LARobotics/LAR-MSL/Code/2023/Images/git_msl_BS.png

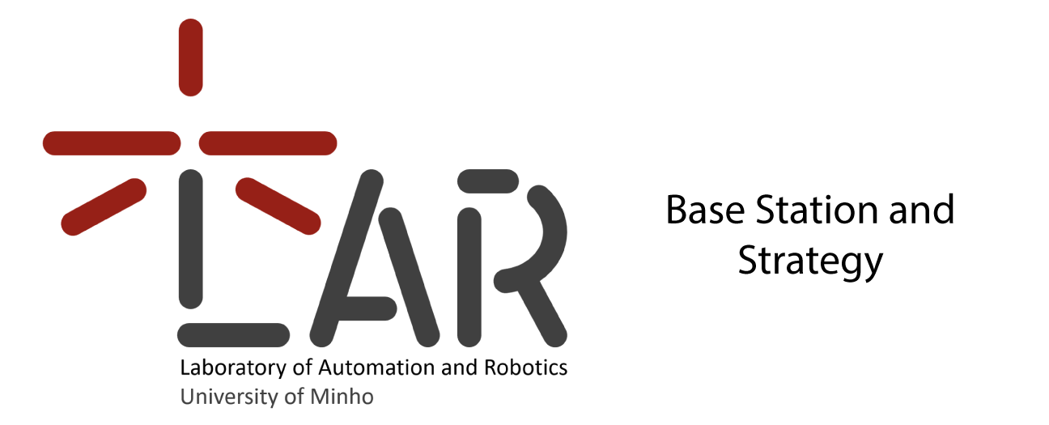
Code/2023/Images/git_msl_BS.png
