LARobotics/LAR-MSL/Code/2023/Images/git_msl_omnivision_pkg.png

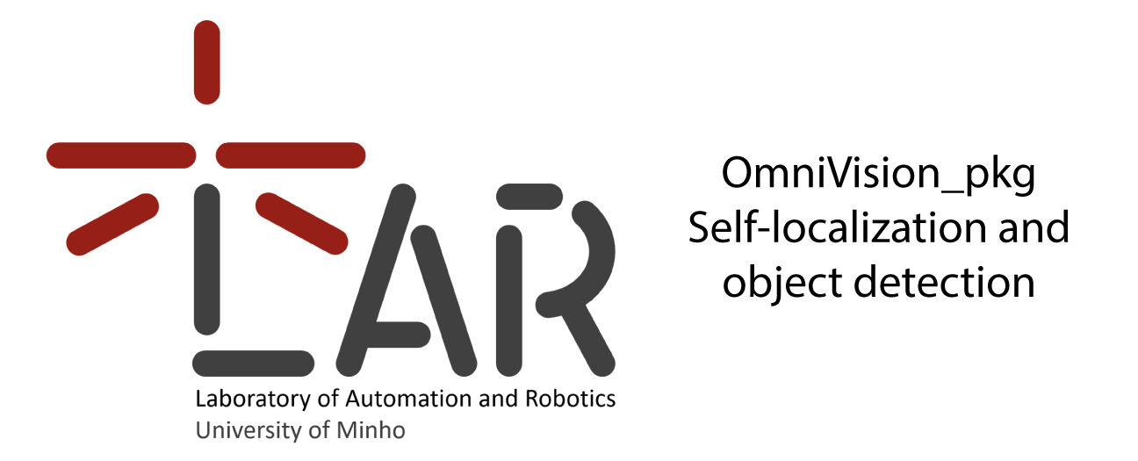
Code/2023/Images/git_msl_omnivision_pkg.png
