LARobotics/LAR-MSL/Code/2023/Player_YOLO/GK_Position/info/plan_scale_1.PNG

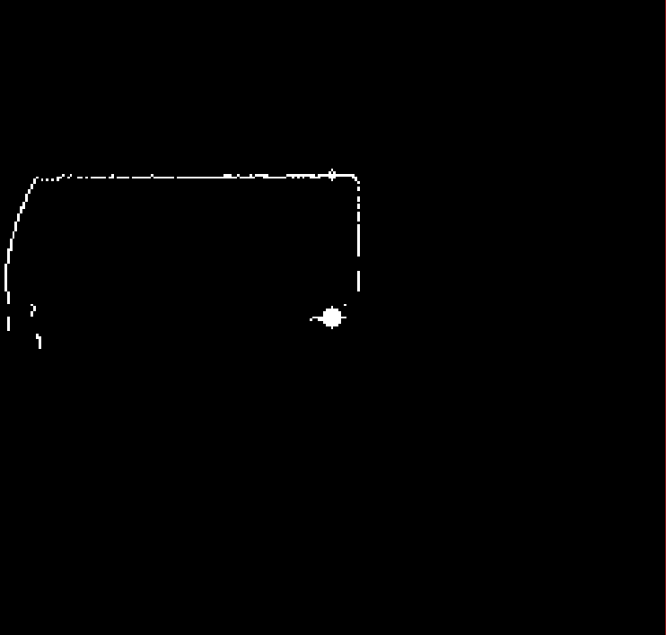
Code/2023/Player_YOLO/GK_Position/info/plan_scale_1.PNG
