LARobotics/LAR-MSL/Code/2023/Player_YOLO/GK_Position/TM/data/escreviaqui.png

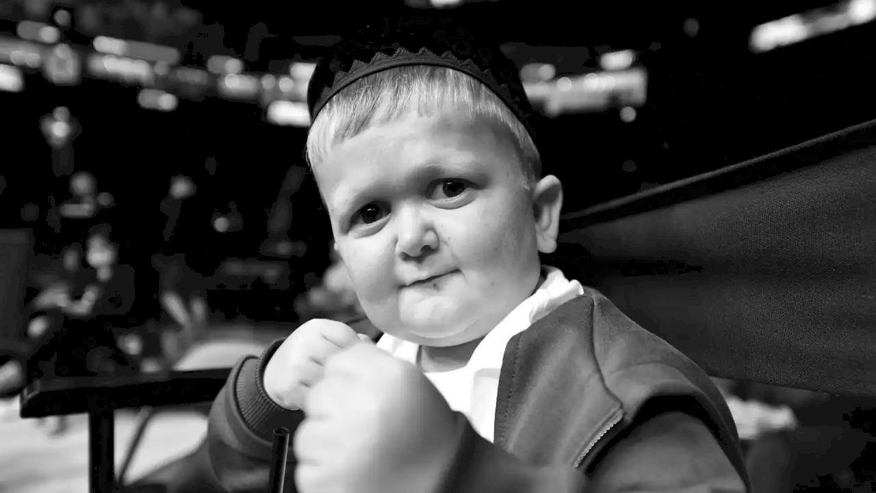
Code/2023/Player_YOLO/GK_Position/TM/data/escreviaqui.png
