LARobotics/LAR-MSL/Code/2023/Player_YOLO/GK_Position/TM/data/template.jpg

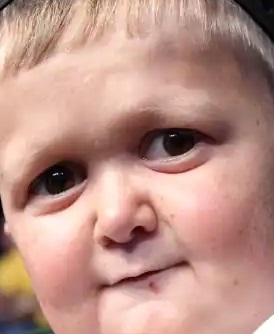
Code/2023/Player_YOLO/GK_Position/TM/data/template.jpg
