LARobotics/LAR-MSL/Code/2023/Player_YOLO/OmniVision_pkg/FIELD.png

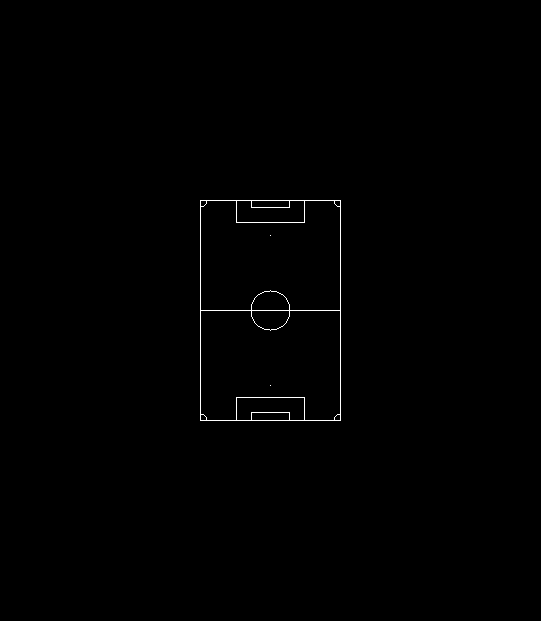
Code/2023/Player_YOLO/OmniVision_pkg/FIELD.png
