LARobotics/LAR-MSL/Code/2023/Player_YOLO/skills/Images/2_frame.png

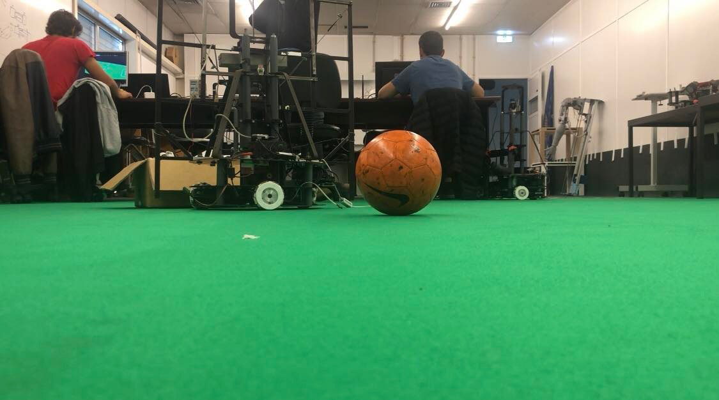
Code/2023/Player_YOLO/skills/Images/2_frame.png
