LARobotics/LAR-MSL/Code/2023/Player_YOLO/skills/Images/FIELD.png

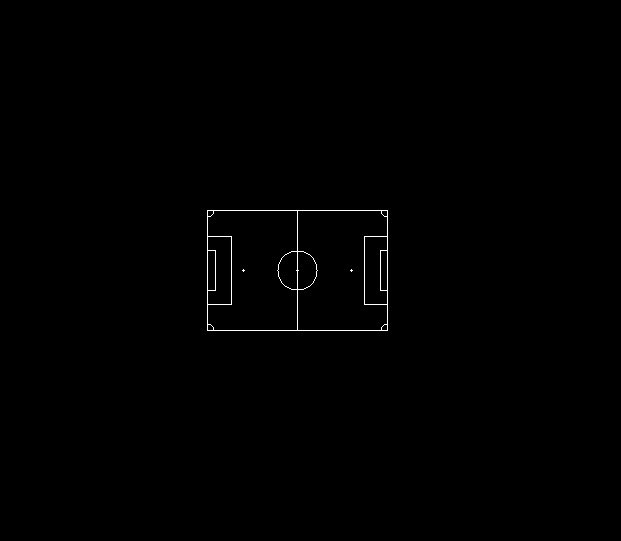
Code/2023/Player_YOLO/skills/Images/FIELD.png
