LARobotics/LAR-MSL/Code/2023/Player_YOLO/skills/Images/Field_Image.jpg

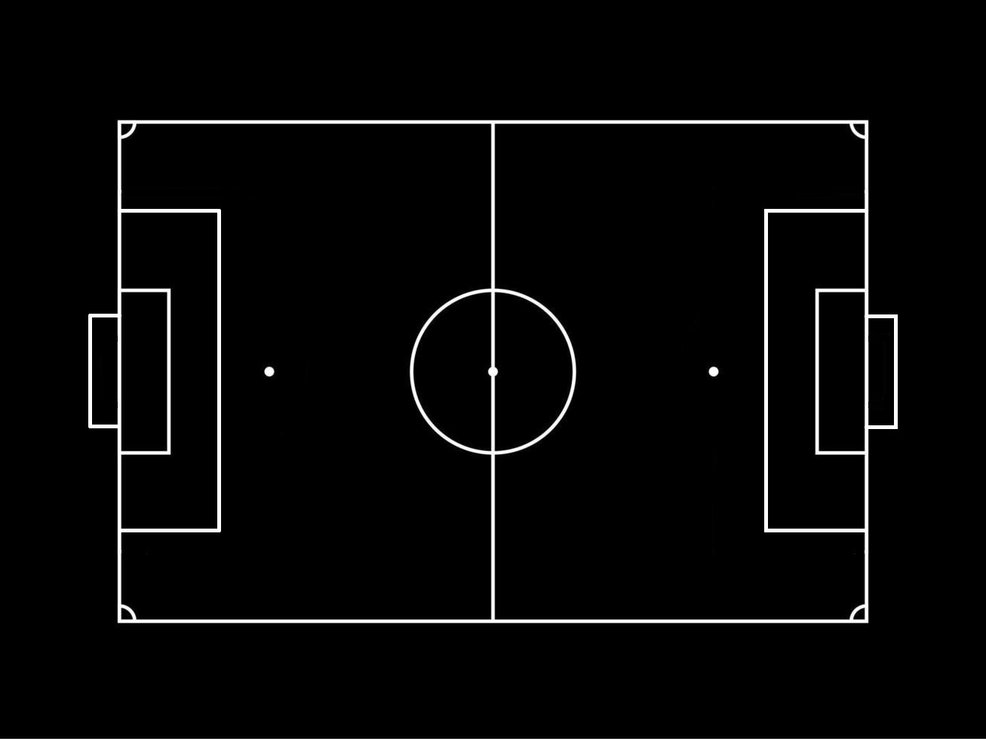
Code/2023/Player_YOLO/skills/Images/Field_Image.jpg
