LARobotics/LAR-MSL/Code/2023/Player_YOLO/skills/Images/goal.png

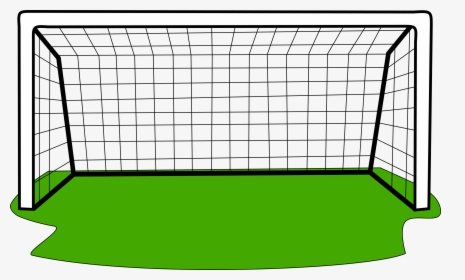
Code/2023/Player_YOLO/skills/Images/goal.png
