LARobotics/LAR-MSL/Simulator/SimuladorWebots/OtherFiles/1B.png

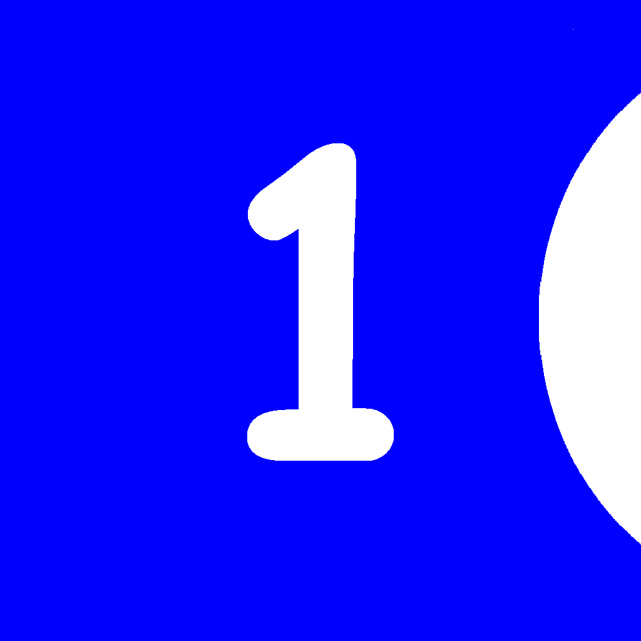
Simulator/SimuladorWebots/OtherFiles/1B.png
