LARobotics/LAR-MSL/Simulator/SimuladorWebots/OtherFiles/2B.png

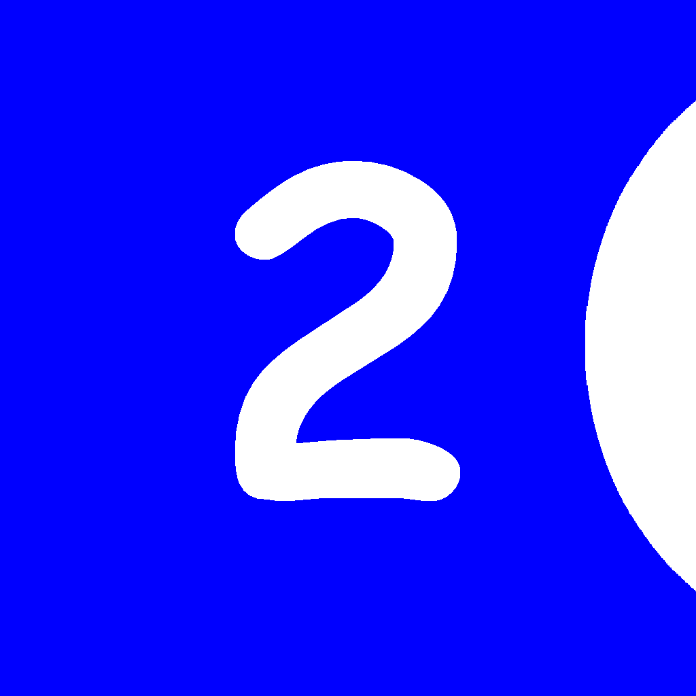
Simulator/SimuladorWebots/OtherFiles/2B.png
