LARobotics/LAR-MSL/Simulator/SimuladorWebots/OtherFiles/3B.png

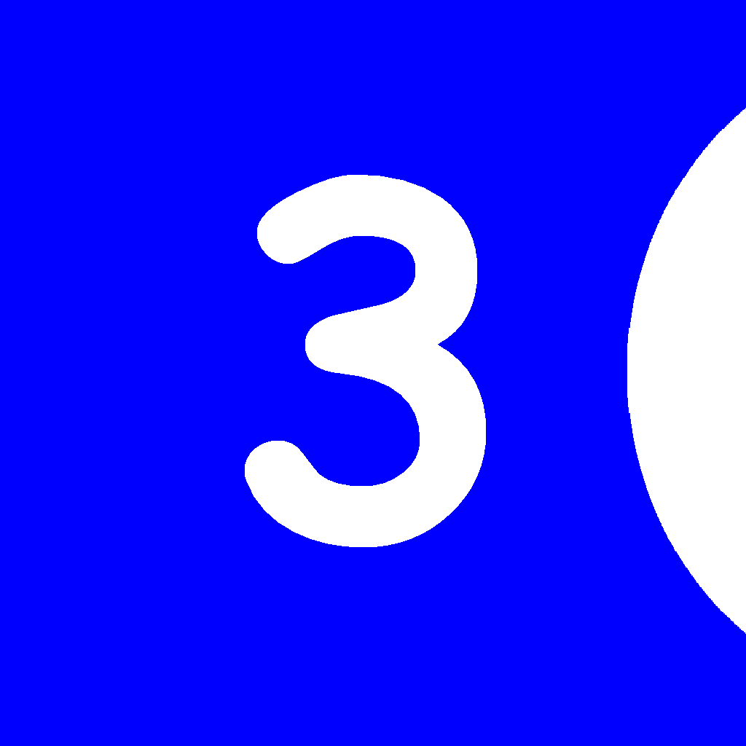
Simulator/SimuladorWebots/OtherFiles/3B.png
