LARobotics/LAR-MSL/Simulator/SimuladorWebots/OtherFiles/4B.png

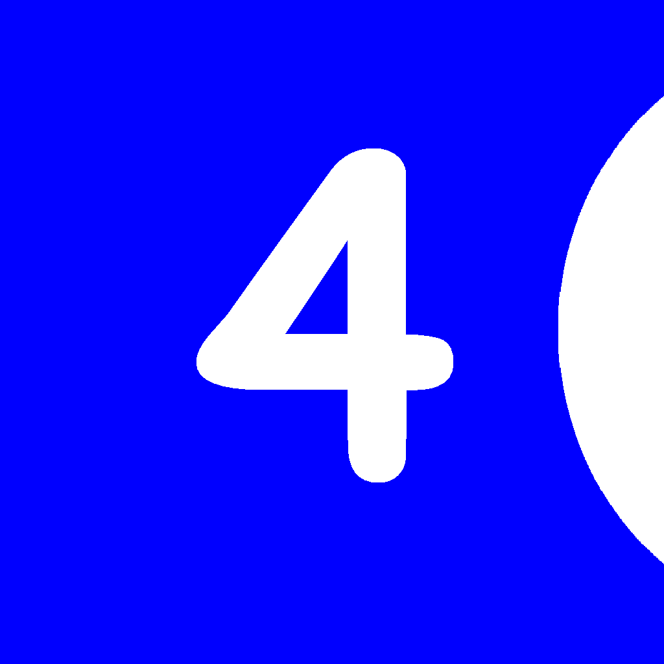
Simulator/SimuladorWebots/OtherFiles/4B.png
