LARobotics/LAR-MSL/Simulator/SimuladorWebots/OtherFiles/5B.png

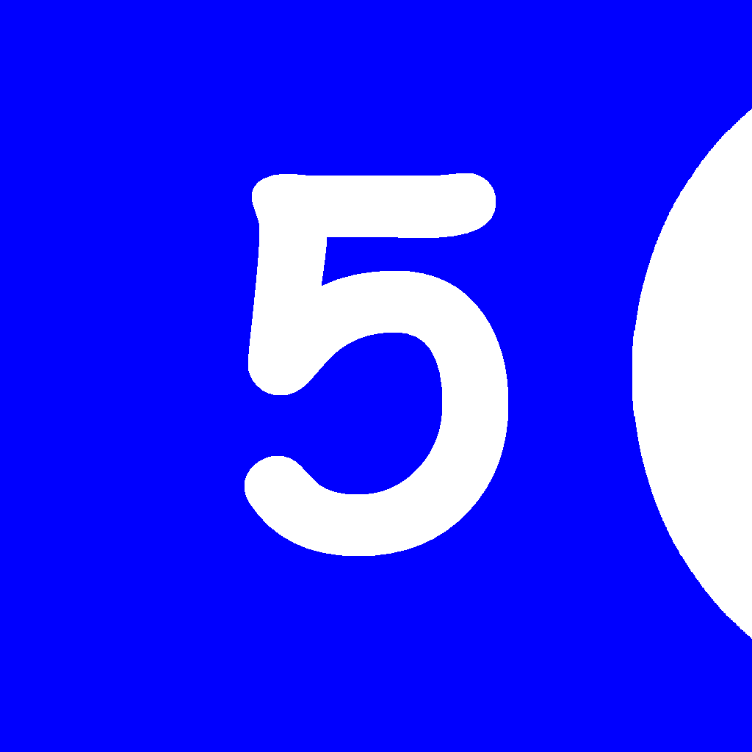
Simulator/SimuladorWebots/OtherFiles/5B.png
