LARobotics/LAR-MSL/Simulator/SimuladorWebots/OtherFiles/Campo2.png

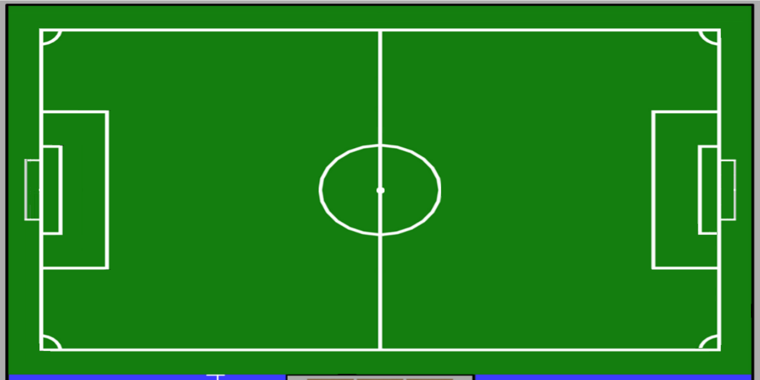
Simulator/SimuladorWebots/OtherFiles/Campo2.png
