LARobotics/LAR-MSL/Simulator/SimuladorWebots/OtherFiles/Texture.png

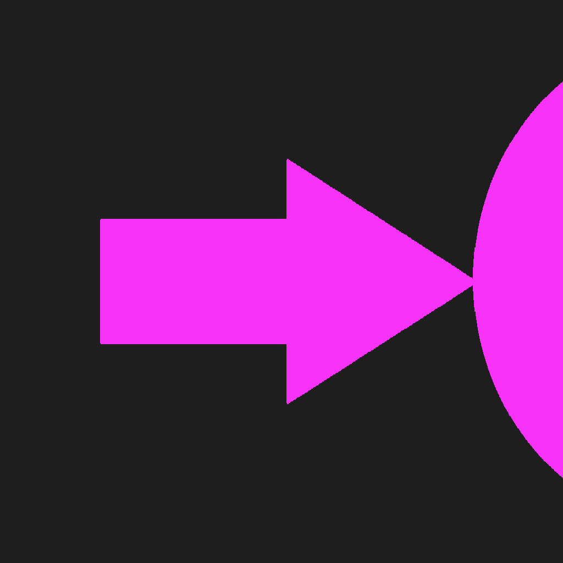
Simulator/SimuladorWebots/OtherFiles/Texture.png
