LARobotics/LAR-MSL/Simulator/SimuladorWebots/OtherProjects/my_supervisor/worlds/.my_supervisor.jpg

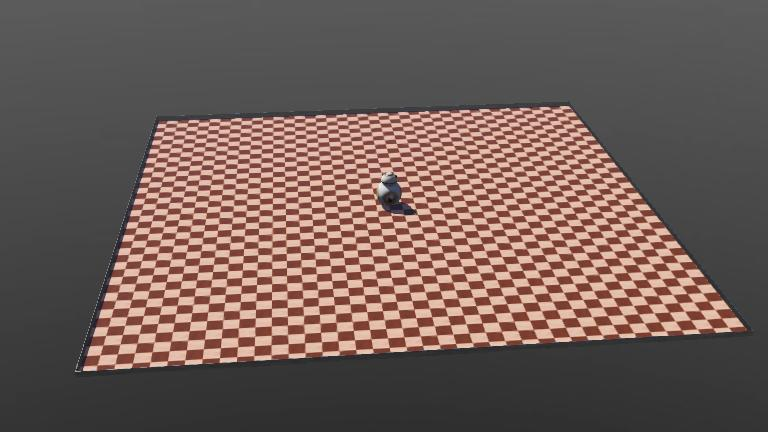
Simulator/SimuladorWebots/OtherProjects/my_supervisor/worlds/.my_supervisor.jpg
