LARobotics/LAR-MSL/Simulator/SimuladorWebots/Simulator/worlds/.SimulatorV2.jpg

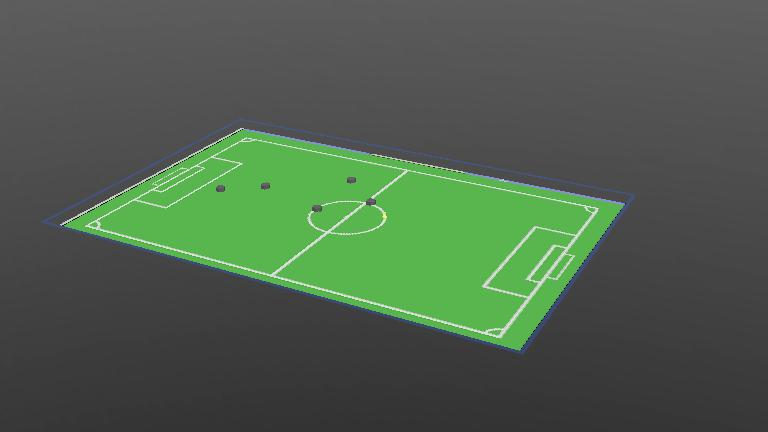
Simulator/SimuladorWebots/Simulator/worlds/.SimulatorV2.jpg
