LARobotics/LAR-MSL/Simulator/SimuladorWebots/Simulator/worlds/.SimulatorV3_Synchonous.jpg

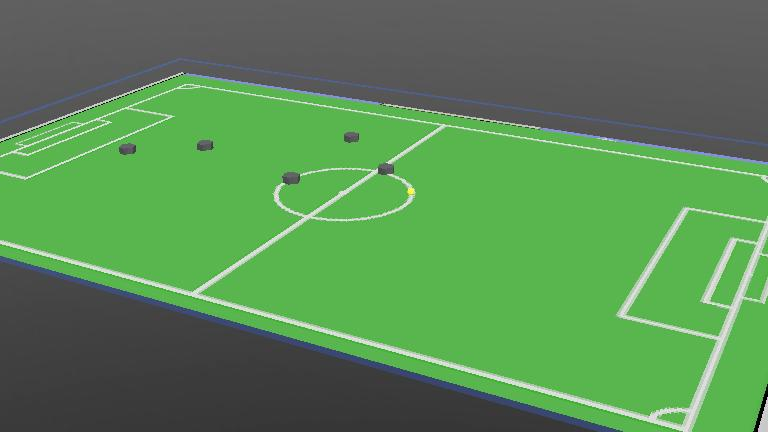
Simulator/SimuladorWebots/Simulator/worlds/.SimulatorV3_Synchonous.jpg
