LARobotics/LAR-MSL/Simulator/SimuladorWebots/Simulator/worlds/.SimulatorV4_SimpleBody_Synchronous.jpg

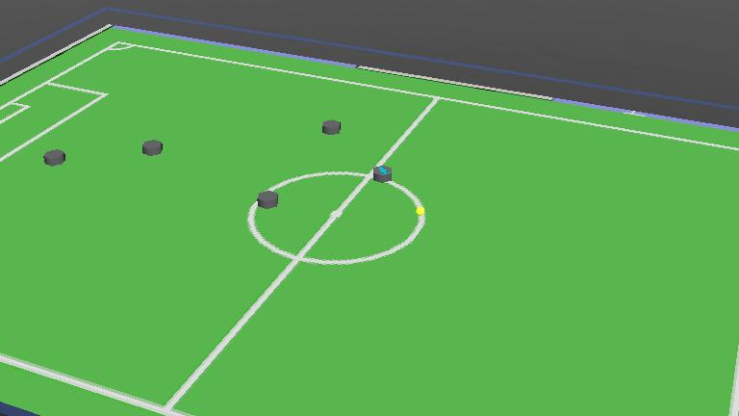
Simulator/SimuladorWebots/Simulator/worlds/.SimulatorV4_SimpleBody_Synchronous.jpg
