LARobotics/LAR-MSL/Simulator/SimuladorWebots/Simulator/worlds/.SimulatorV4_SimpleBodyA_Synchronous.jpg

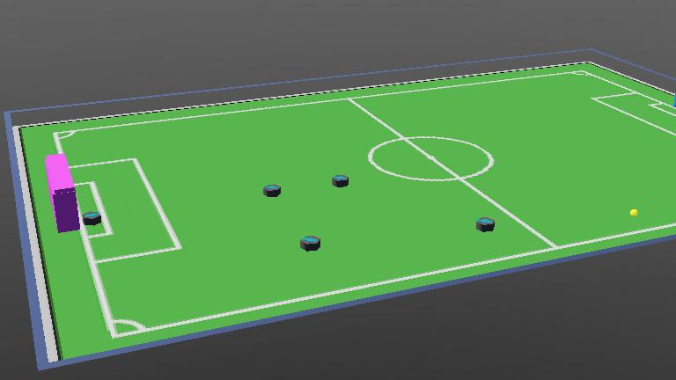
Simulator/SimuladorWebots/Simulator/worlds/.SimulatorV4_SimpleBodyA_Synchronous.jpg
