LARobotics/LAR-MSL/Simulator/SimuladorWebots/Simulator/worlds/.SimulatorV4_SimpleBodyA_Synchronous_AFConnector.jpg

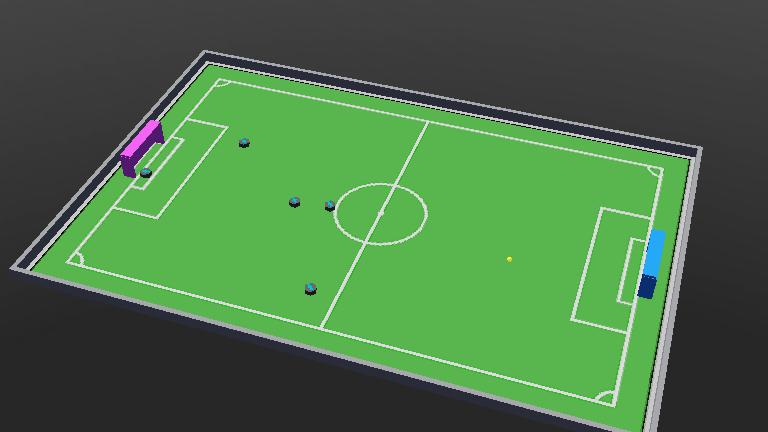
Simulator/SimuladorWebots/Simulator/worlds/.SimulatorV4_SimpleBodyA_Synchronous_AFConnector.jpg
