LARobotics/LAR-MSL/Simulator/SimuladorWebots/Simulator/worlds/.SimulatorV5.jpg

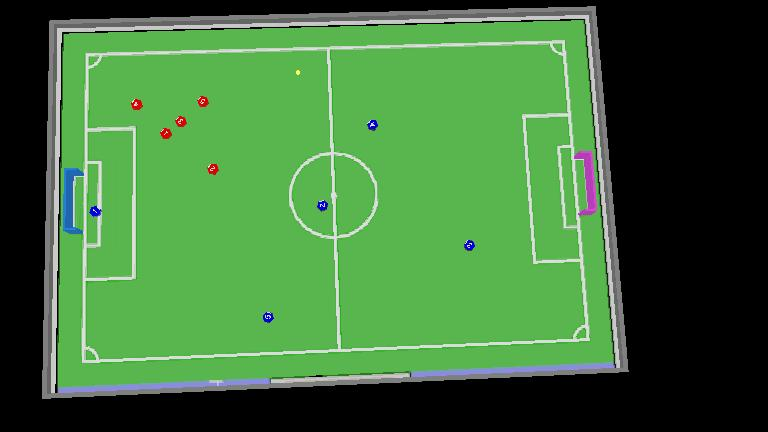
Simulator/SimuladorWebots/Simulator/worlds/.SimulatorV5.jpg
