LARobotics/LAR-MSL/Simulator/SimuladorWebots/Simulator/worlds/.SimulatorV6.jpg

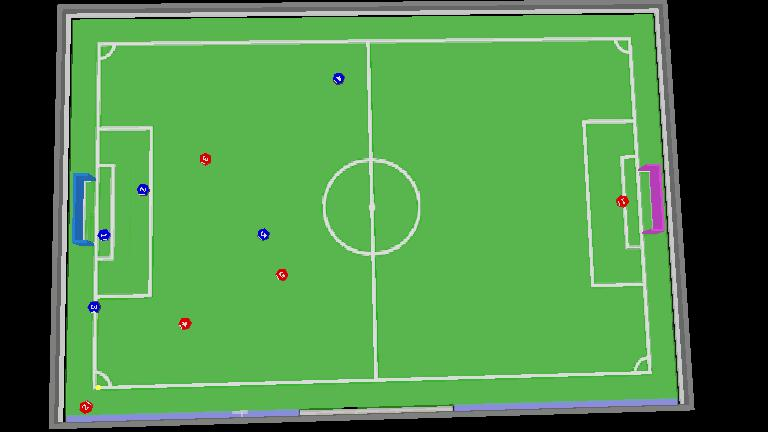
Simulator/SimuladorWebots/Simulator/worlds/.SimulatorV6.jpg
