LARobotics/LAR-MSL/Simulator/SimuladorWebots/Simulator/worlds/.WorkingRobot_SuperVisor.jpg

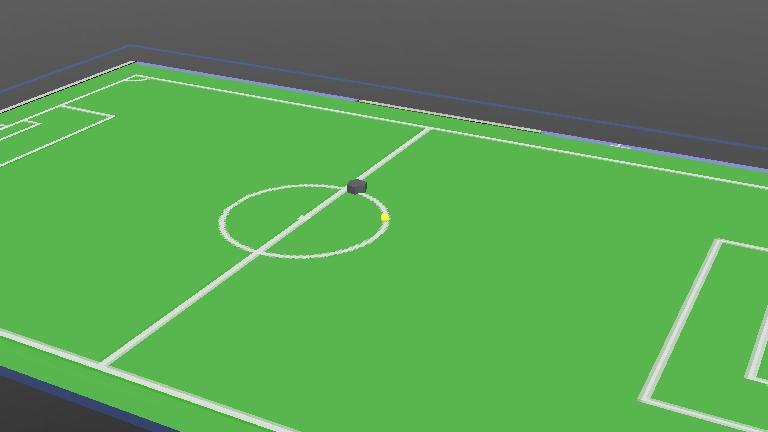
Simulator/SimuladorWebots/Simulator/worlds/.WorkingRobot_SuperVisor.jpg
