LARobotics/LAR-MSL/Simulator/otherSimulationFiles/MSLSimulatorBody.stl

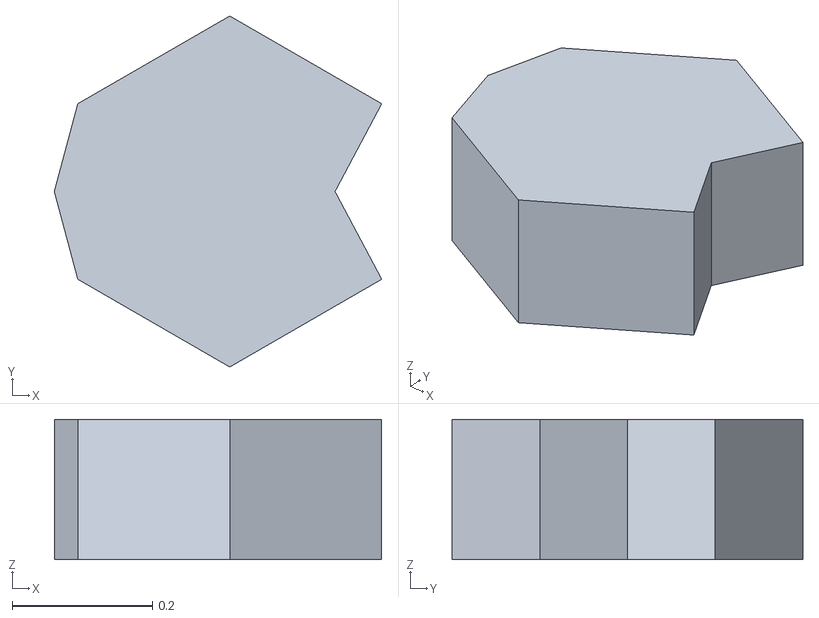
[picture p68: CAD file, 2024-02-29]
Simulator/otherSimulationFiles/MSLSimulatorBody.stl
0.467 x 0.5 x 0.2
