LARobotics/LAR-MSL/Simulator/SimuladorCoppelia/Robo.stl

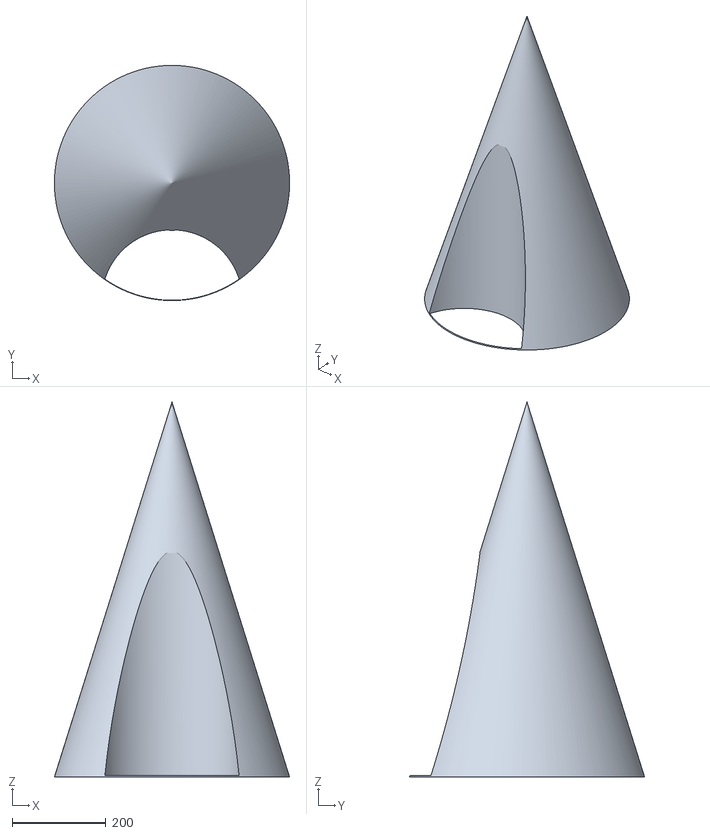
[picture p69: CAD file, 2024-02-29]
Simulator/SimuladorCoppelia/Robo.stl
501.8 x 501.8 x 800.0
