LARobotics/LAR-MSL/Simulator/SimuladorWebots/OtherFiles/simplify_RobotV2.obj

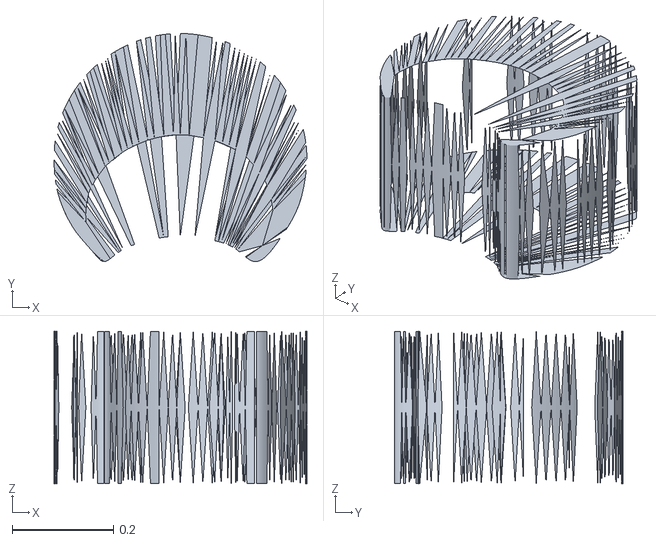
[picture p70: CAD file, 2024-02-29]
Simulator/SimuladorWebots/OtherFiles/simplify_RobotV2.obj
0.499 x 0.45 x 0.3
