LARobotics/LAR-MSL/3D Cads/Dribbler/DribblerSupport.obj

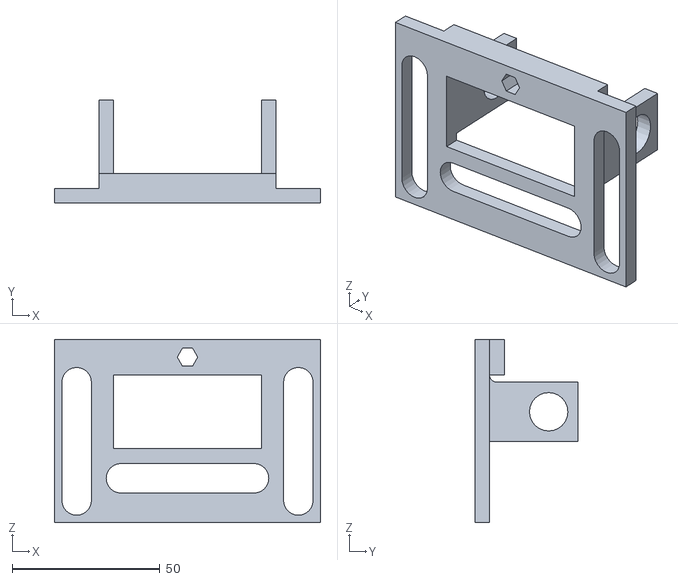
[picture p71: CAD file, 2023-03-16]
3D Cads/Dribbler/DribblerSupport.obj
90.0 x 35.0 x 62.0
