LARobotics/LAR-MSL/3D Cads/Kinect Support/KinectBox.obj

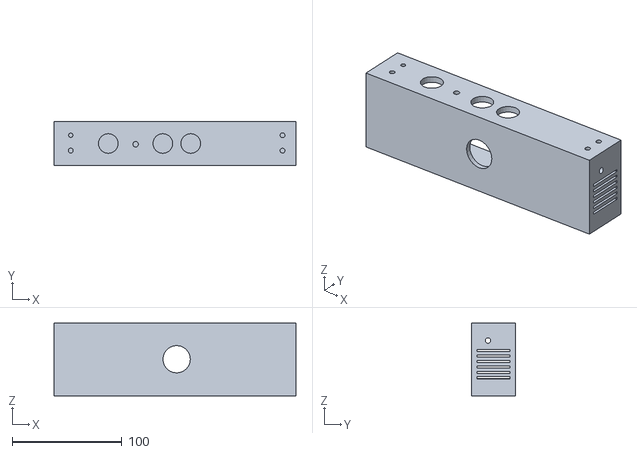
[picture p72: CAD file, 2023-03-16]
3D Cads/Kinect Support/KinectBox.obj
221.0 x 40.0 x 66.5
