LARobotics/LAR-MSL/3D Cads/Structure/TopPlate.obj

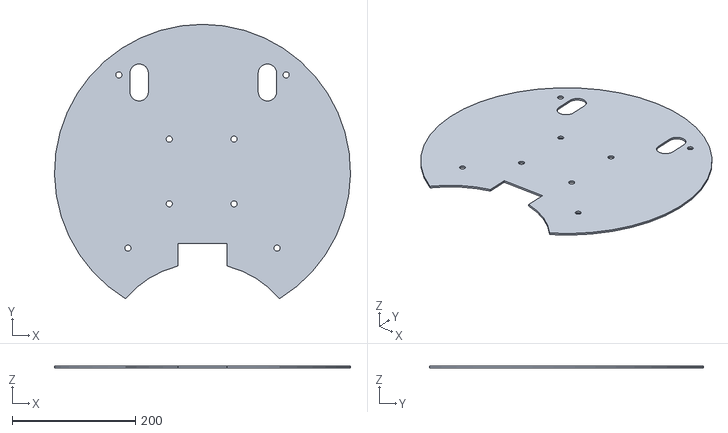
[picture p73: CAD file, 2023-03-16]
3D Cads/Structure/TopPlate.obj
480.0 x 444.9 x 3.00
