LARobotics/LAR-MSL/Code/2023/Calibration-Tools/src/FIELD2.png

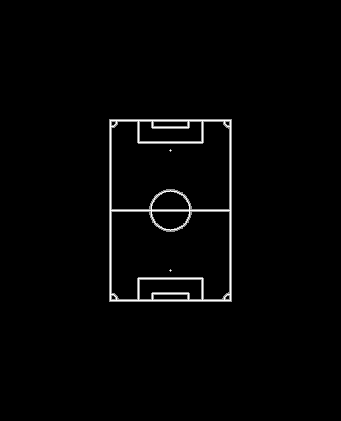
Code/2023/Calibration-Tools/src/FIELD2.png
