LARobotics/LAR-MSL/Code/2023/Calibration-Tools/src/Robot5_bola_10.png

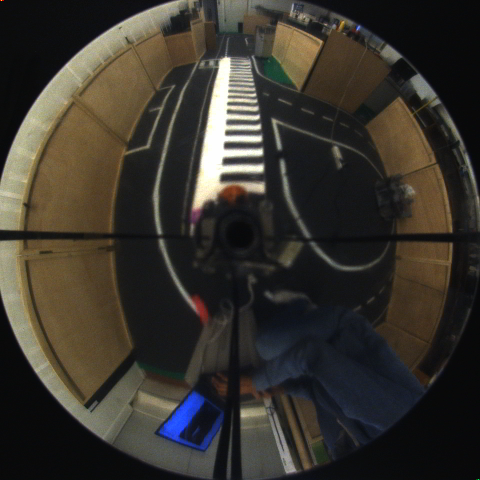
Code/2023/Calibration-Tools/src/Robot5_bola_10.png
