LARobotics/LAR-MSL/Simulator/OutrosTests/omniwhels_dance/worlds/.omni_wheels.jpg

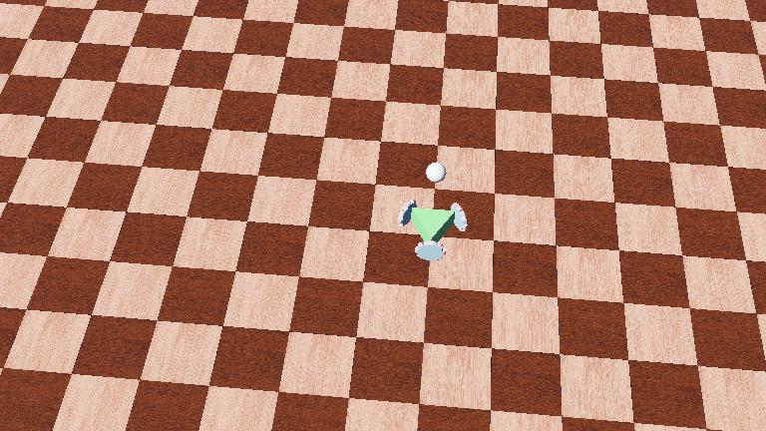
Simulator/OutrosTests/omniwhels_dance/worlds/.omni_wheels.jpg
