LARobotics/LAR-MSL/Simulator/OutrosTests/WebotsOmni/worlds/.omni_wheels.jpg

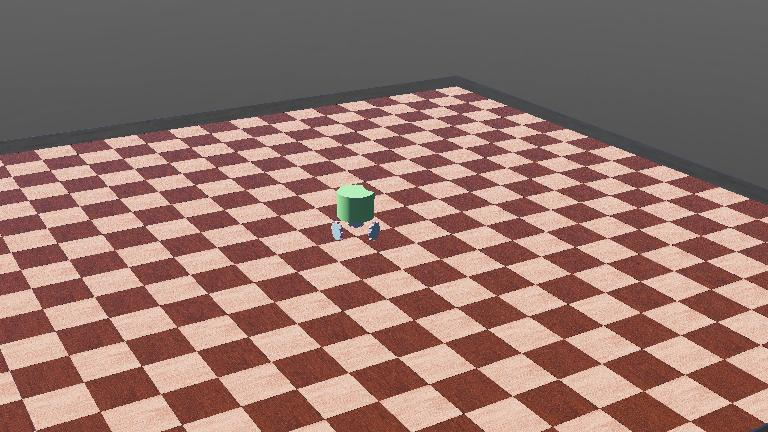
Simulator/OutrosTests/WebotsOmni/worlds/.omni_wheels.jpg
