LARobotics/LAR-MSL/Simulator/SimuladorWebots/Simulator/worlds/.SimulatorV4_SimpleObjectTest.jpg

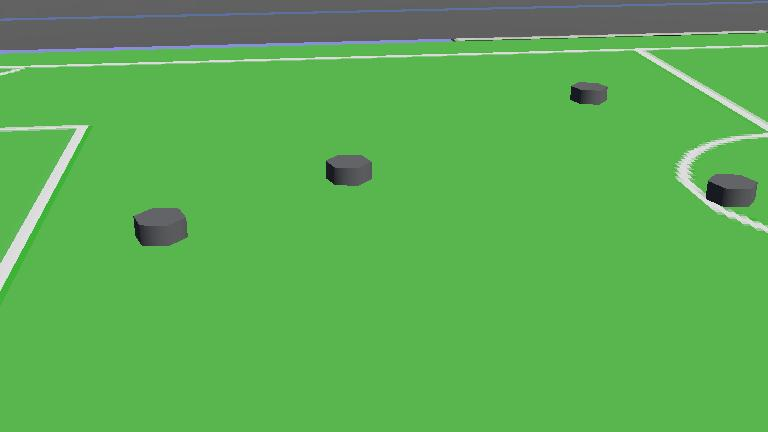
Simulator/SimuladorWebots/Simulator/worlds/.SimulatorV4_SimpleObjectTest.jpg
